Humanlab44-Org/Interface_Adaptative/programme/include/myStructs.h

/*
Nom du fichier : myStruct.h
Auteur : Yann Cesbron  (yann@cesbron.org)
Date de création : 4 avril 2023
Licence :  Creative Commons BY-NC-SA
*/

//#pragma once
// ------------ system configuration file
struct Configuration
{
    int version;
    int button_number;
    String BLEdevicename;
    String BLEdeviceManufacturer;
    String WIFIssid;
    String WIFIpassword;
};
